GusLafer/FunbioGrupo13/Documentos/Certificados Advanced Onshape/julio-cerna-8390236b-1912-404f-a9d6-00e211f68d9f-certificate.pdf

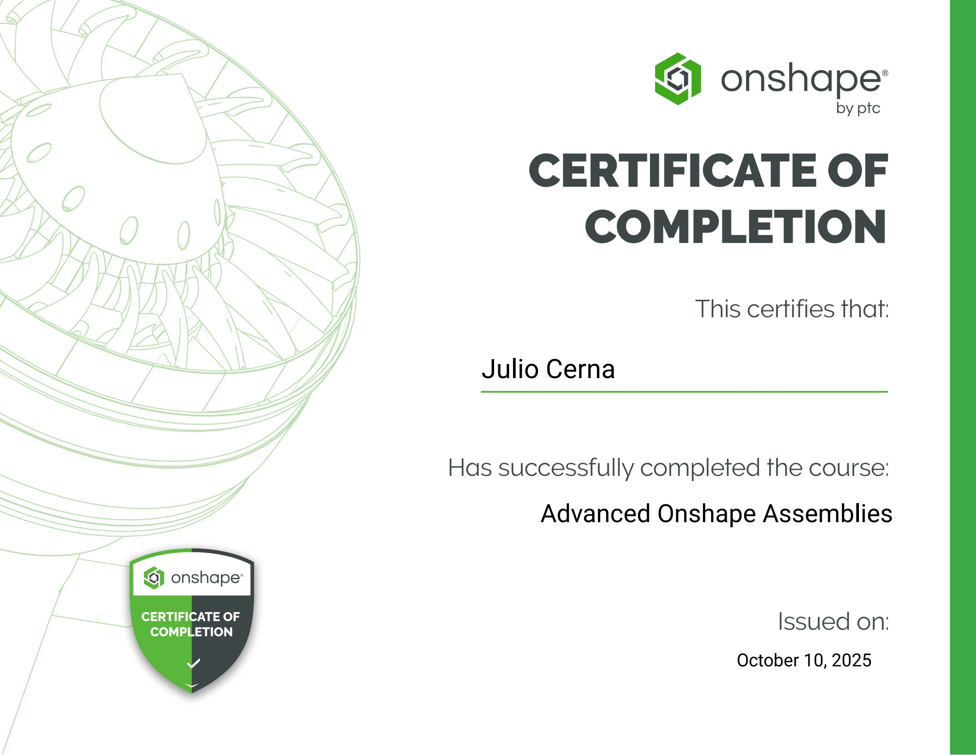
[picture p40: page 1]

Julio Cerna

Advanced Onshape Assemblies

October 10, 2025
