GusLafer/FunbioGrupo13/Documentos/Certificados Advanced Onshape/anyelo-armando-castillo-mayta-ede3d43d-8260-4bd8-9333-eddac3b828b3-certificate.pdf

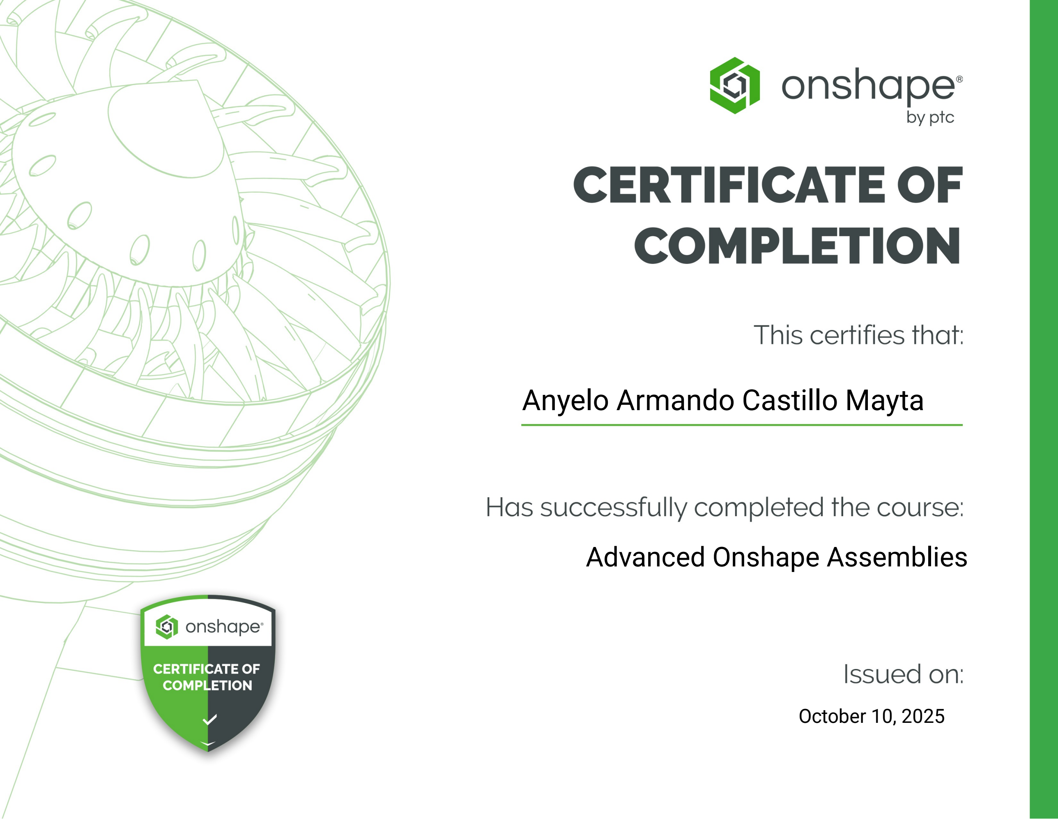
[picture p41: page 1]

Anyelo Armando Castillo Mayta

Advanced Onshape Assemblies

October 10, 2025
