GusLafer/FunbioGrupo13/Documentos/Certificados Advanced Onshape/cristhian-leonardo-castillo-zapata-e07da1f7-74c5-4922-b772-d9635f6dc2e9-certificate.pdf

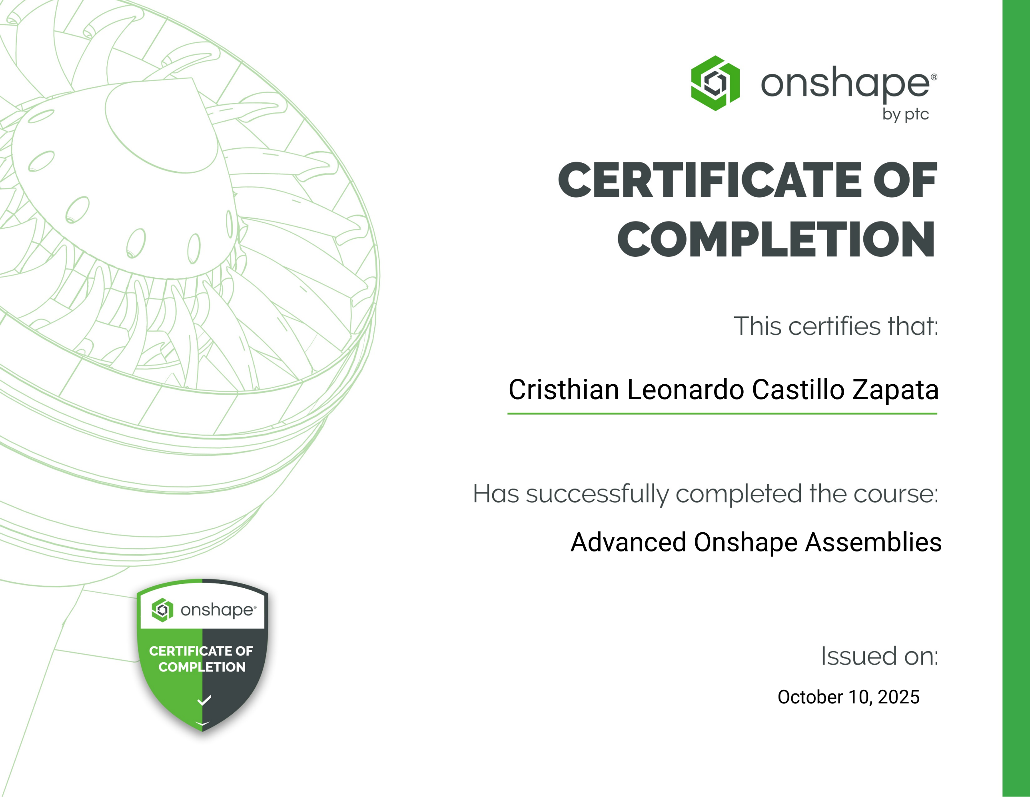
[picture p42: page 1]

Cristhian Leonardo Castillo Zapata

Advanced Onshape Assemblies

October 10, 2025
