GusLafer/FunbioGrupo13/Documentos/Certificados Advanced Onshape/Cuentas Ferreñan, Bonnie Camila.pdf

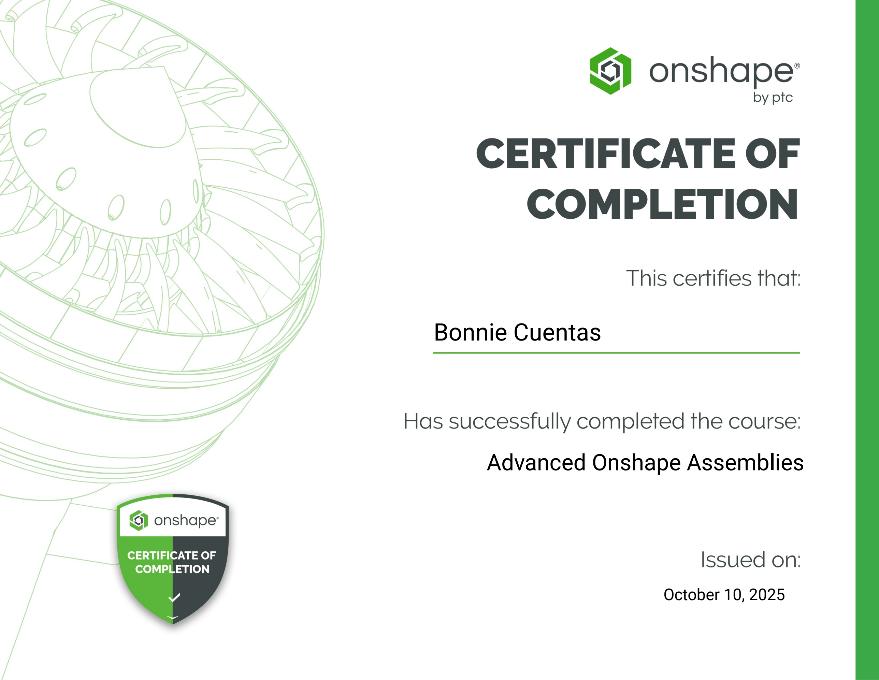
[picture p43: page 1]

Bonnie Cuentas

Advanced Onshape Assemblies

October 10, 2025
