GusLafer/FunbioGrupo13/Documentos/Certificados Advanced Onshape/karla-garca-4118d52e-07bf-4f01-b46d-117be6cba066-certificate.pdf

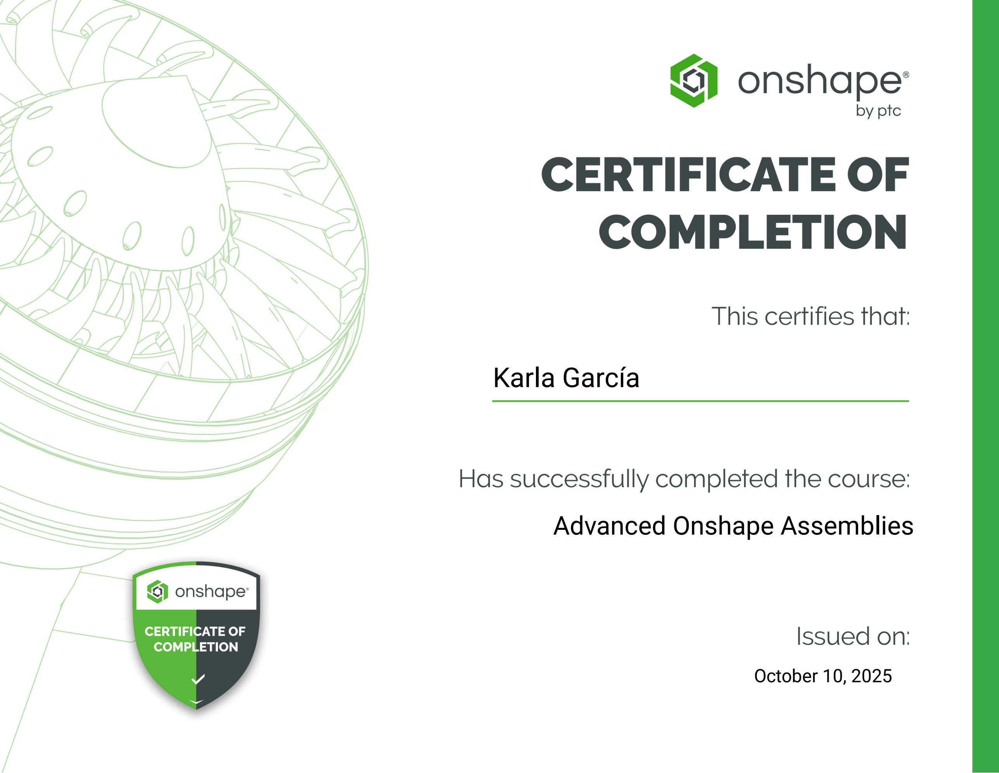
[picture p44: page 1]

Karla García

Advanced Onshape Assemblies

October 10, 2025
