GusLafer/FunbioGrupo13/Documentos/Certificados Advanced Onshape/gustavo-rodolfo-fernandez-baca-lara-8739a996-e9ae-4892-a879-7a38d6f8b901-certificate.pdf

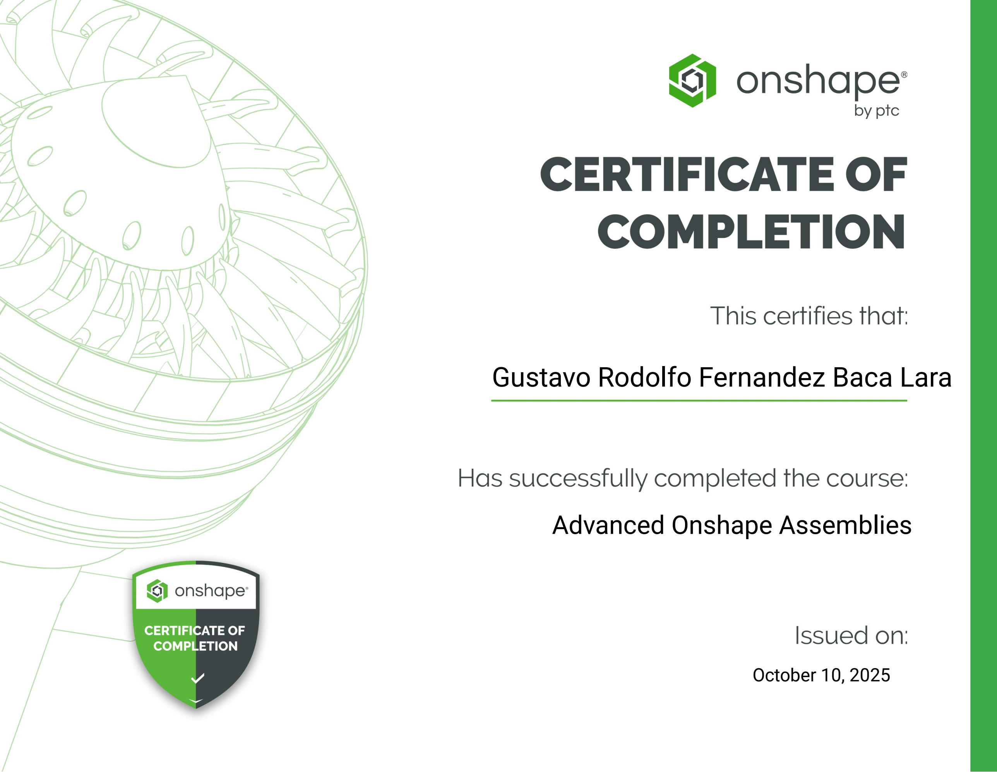
[picture p45: page 1]

Gustavo Rodolfo Fernandez Baca Lara

Advanced Onshape Assemblies

October 10, 2025
