GusLafer/FunbioGrupo13/Documentos/TALLER DE MODELADO 3D Fundamentos de CAD/gustavo-rodolfo-fernandez-baca-lara-7baae7e9-768c-4d42-a333-d1a9afca94c1-certificate.pdf

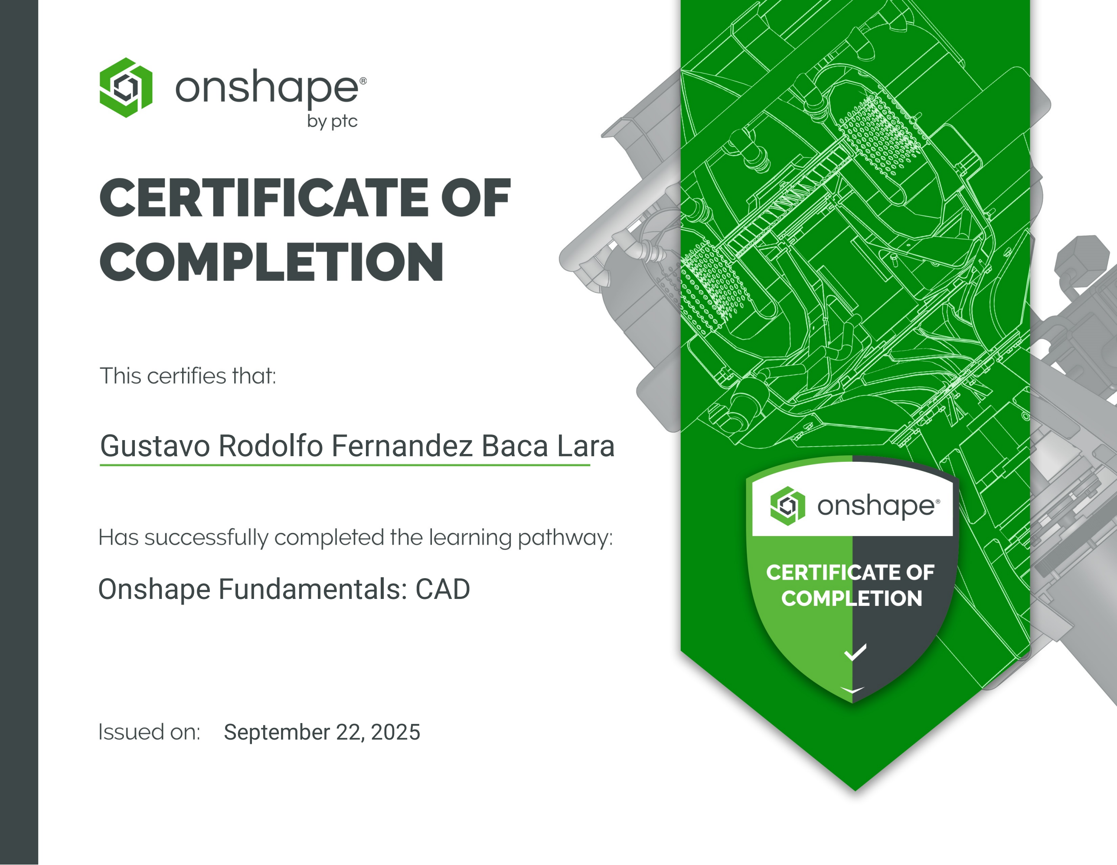
[picture p46: page 1]

Onshape Fundamentals: CAD

September 22, 2025

Gustavo Rodolfo Fernandez Baca Lara
