GusLafer/FunbioGrupo13/Documentos/TALLER DE MODELADO 3D Fundamentos de CAD/Cuentas Ferreñan, Bonnie Camila.pdf

Onshape Fundamentals: CAD

September 21, 2025

Bonnie Cuentas

Bonnie Cuentas

Introduction to Sketching

September 21, 2025

Bonnie Cuentas

Introduction to Part Studios

September 21, 2025

Bonnie Cuentas

September 21, 2025

Multi-Part Part Studios

Bonnie Cuentas

September 21, 2025

Onshape Assemblies

Bonnie Cuentas

September 21, 2025

Detailed Drawings
