GusLafer/FunbioGrupo13/Documentos/TALLER DE MODELADO 3D Fundamentos de CAD/karla-garca-a77ddb6f-bb4a-4f3d-a21e-6f4486621819-certificate.pdf

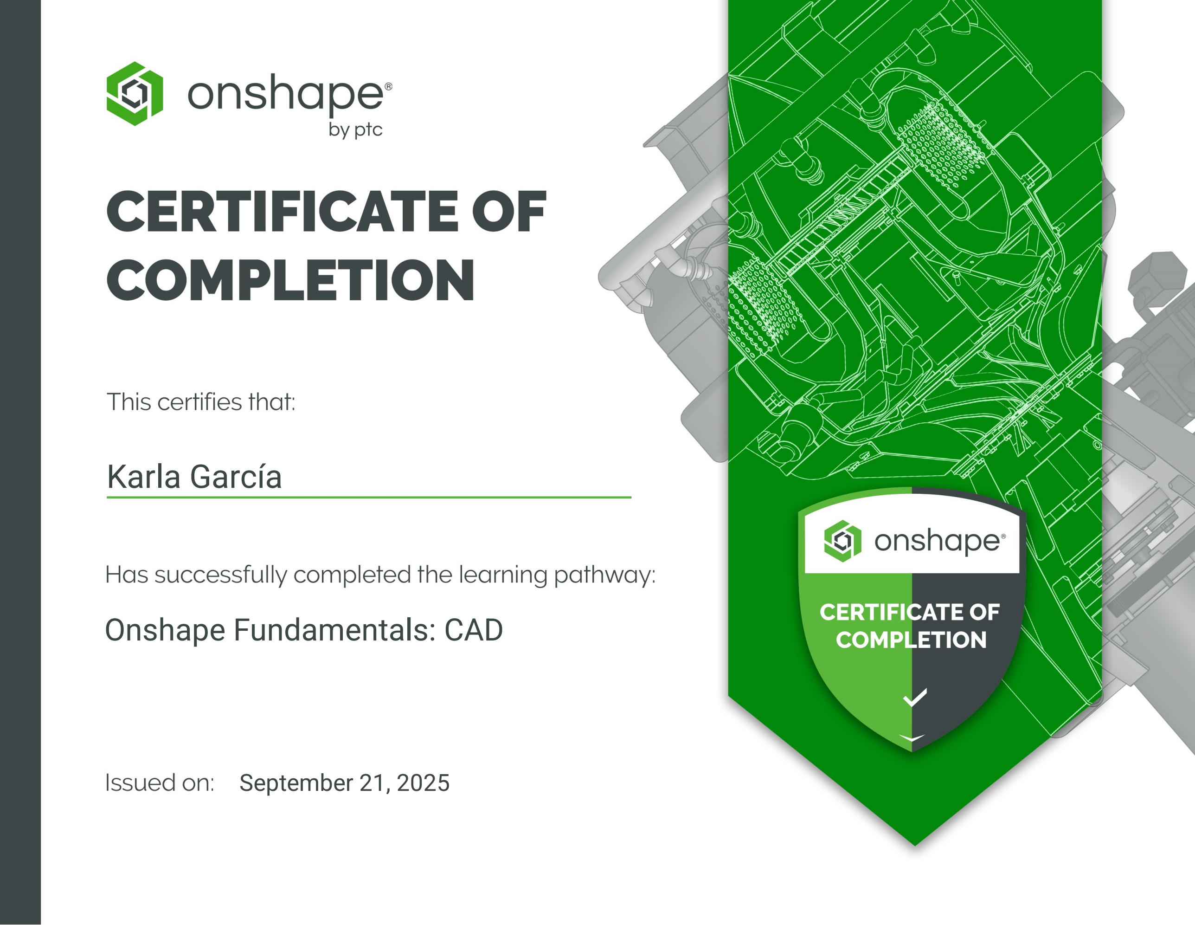
[picture p47: page 1]

Onshape Fundamentals: CAD

September 21, 2025

Karla García
