GusLafer/FunbioGrupo13/Documentos/TALLER DE MODELADO 3D Fundamentos de CAD/anyelo-armando-castillo-mayta-certificate.pdf

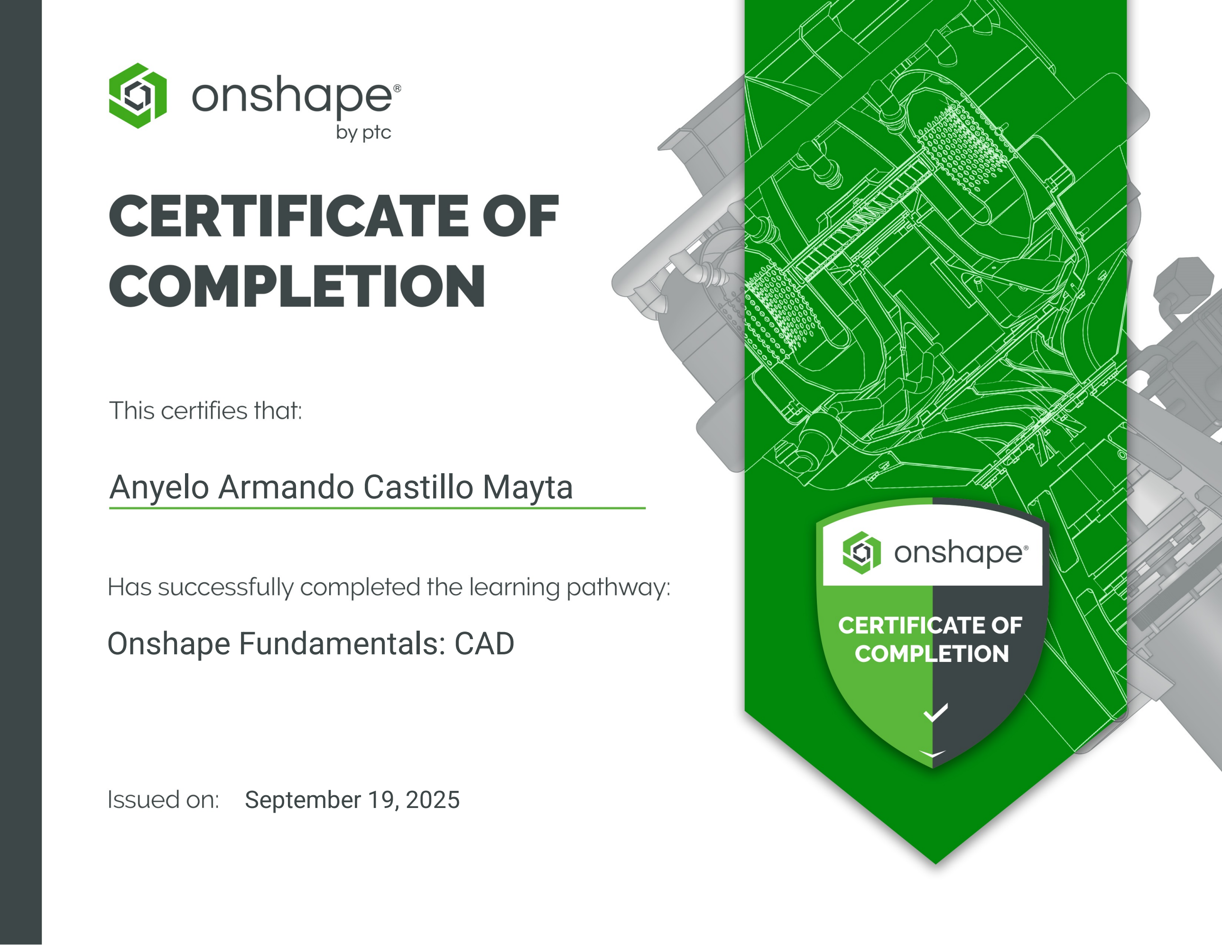
[picture p48: page 1]

Onshape Fundamentals: CAD

September 19, 2025

Anyelo Armando Castillo Mayta
