GusLafer/FunbioGrupo13/Documentos/TALLER DE MODELADO 3D Fundamentos de CAD/julio_cerna_acosta.pdf

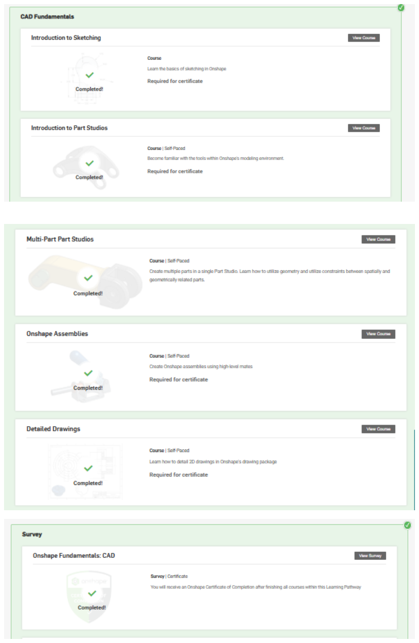
[picture p81: page 1]
